ilPez00/cyclops-wearable/cad/pendant_preview.png

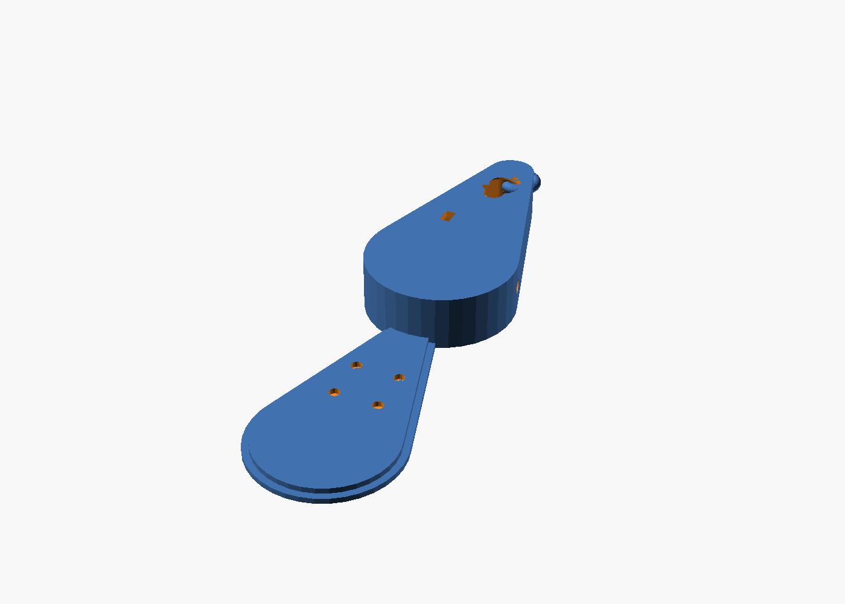
cad/pendant_preview.png
