ilPez00/cyclops-wearable/cad/preview_xiao.png

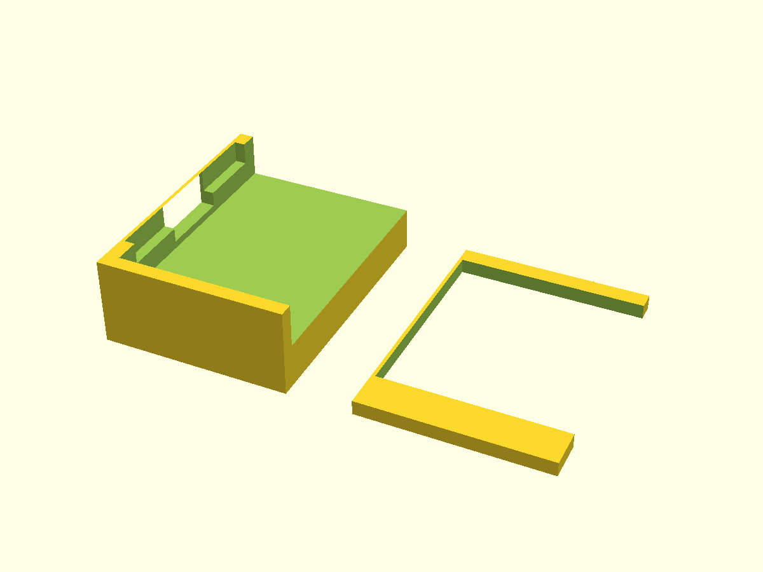
cad/preview_xiao.png
