ilPez00/cyclops-wearable/cad/preview_xiao_v1_pebble.png

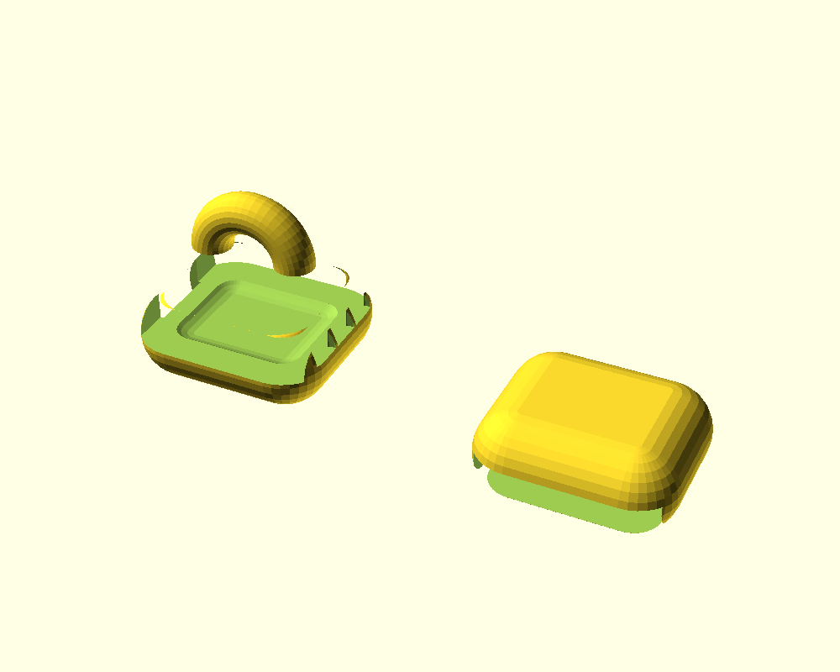
cad/preview_xiao_v1_pebble.png
