ilPez00/cyclops-wearable/cad/preview_xiao_v2_leaf.png

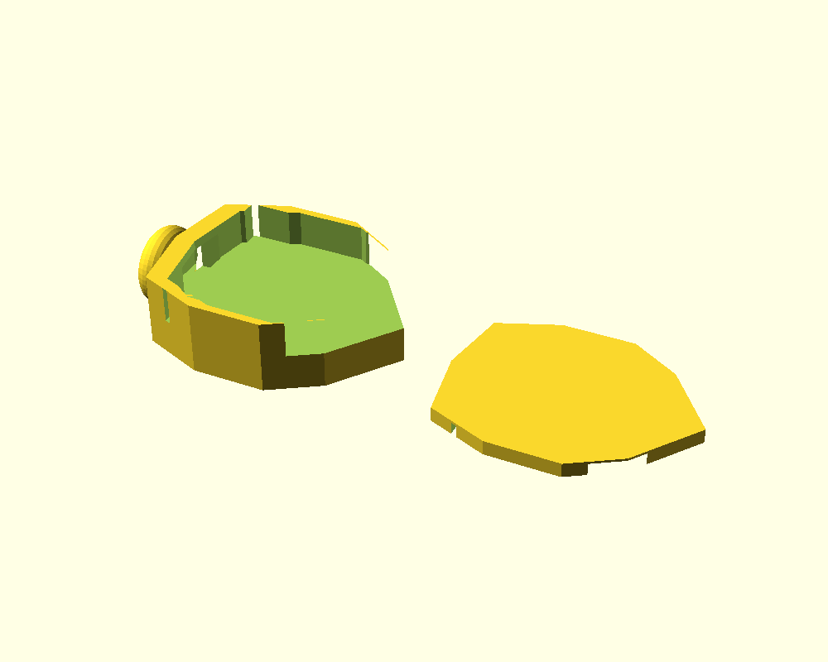
cad/preview_xiao_v2_leaf.png
