ilPez00/cyclops-wearable/cad/preview_xiao_v3_gem.png

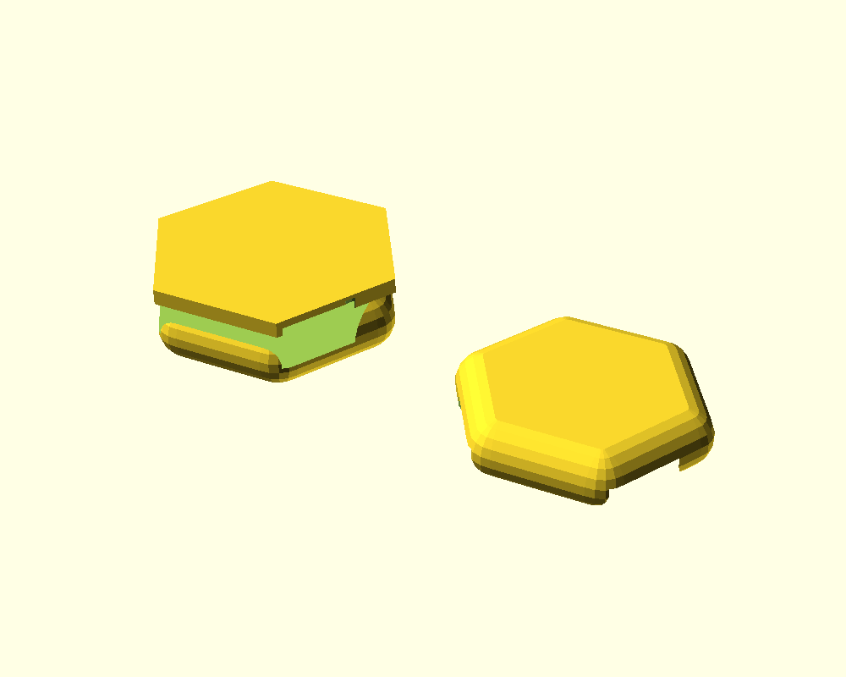
cad/preview_xiao_v3_gem.png
