ilPez00/cyclops-wearable/cad/preview_xiao_v4_temple.png

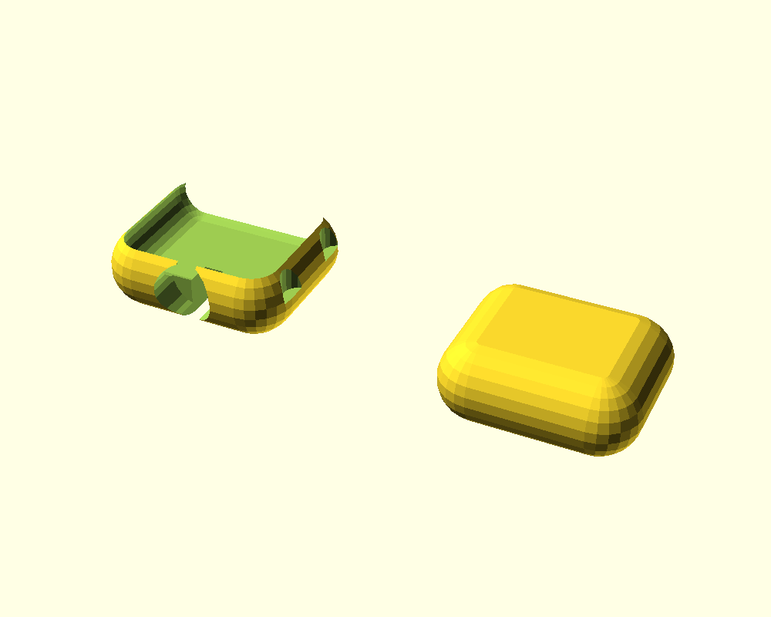
cad/preview_xiao_v4_temple.png
