ilPez00/cyclops-wearable/cad/variants/preview_xiao_pebble.png

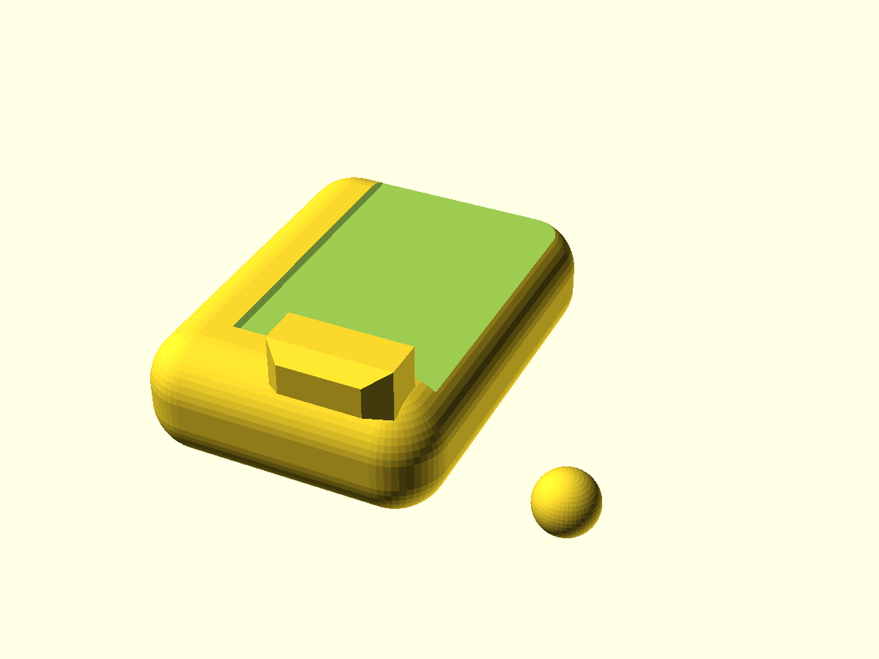
cad/variants/preview_xiao_pebble.png
