ilPez00/cyclops-wearable/cad/variants/preview_xiao_skeleton.png

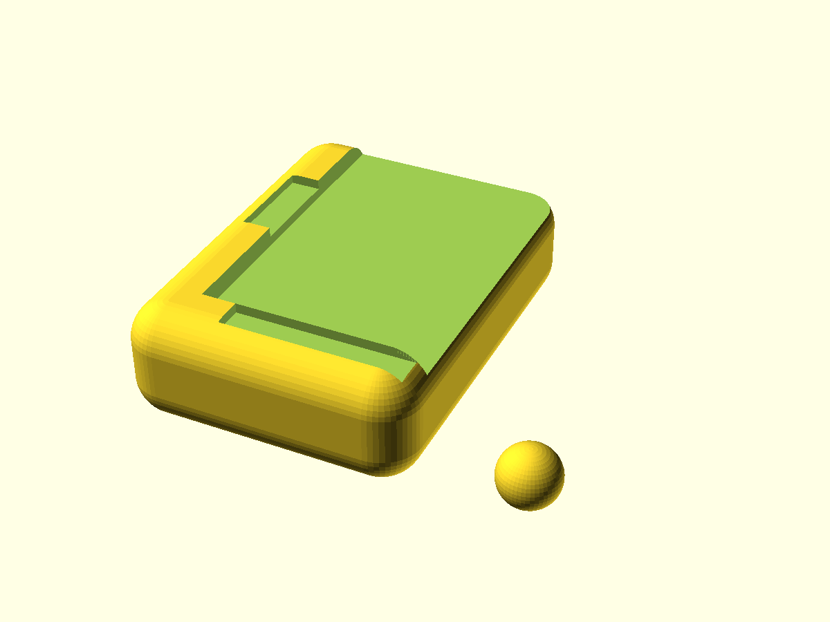
cad/variants/preview_xiao_skeleton.png
