ilPez00/cyclops-wearable/cad/variants/preview_xiao_tech.png

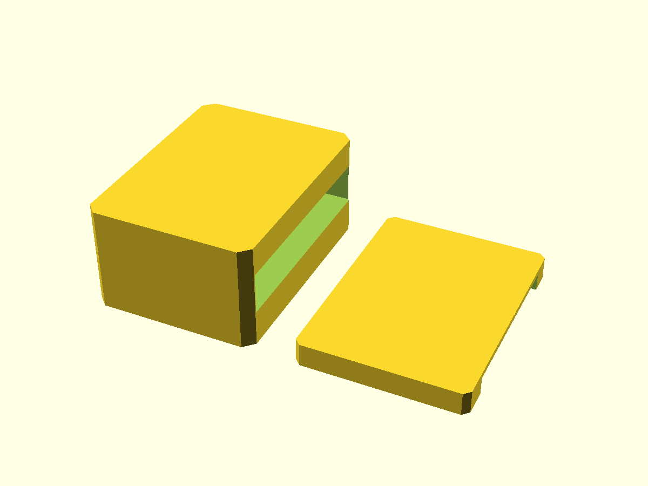
cad/variants/preview_xiao_tech.png
