ilPez00/cyclops-wearable/cad/stl/pendant_v3_antenna_body.stl

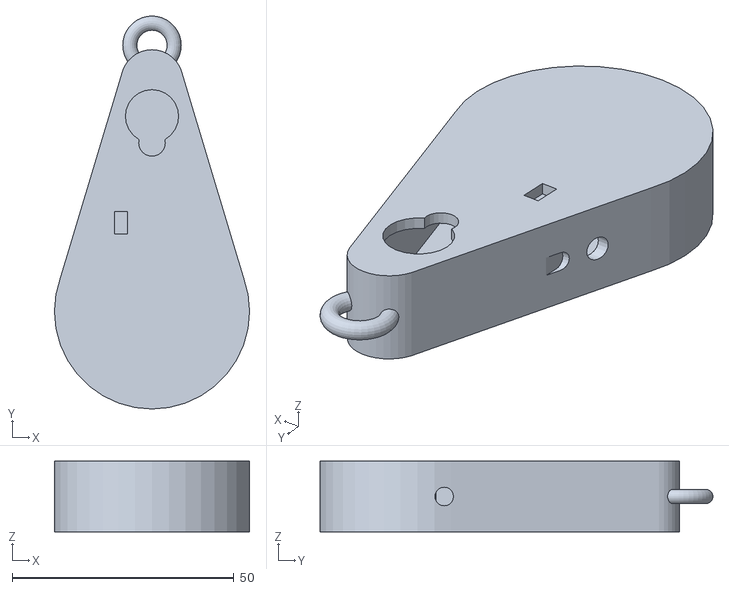
[picture p27: CAD file, 2026-07-10]
cad/stl/pendant_v3_antenna_body.stl
44.0 x 88.6 x 16.0
