ilPez00/cyclops-wearable/cad/stl/pendant_cap.stl

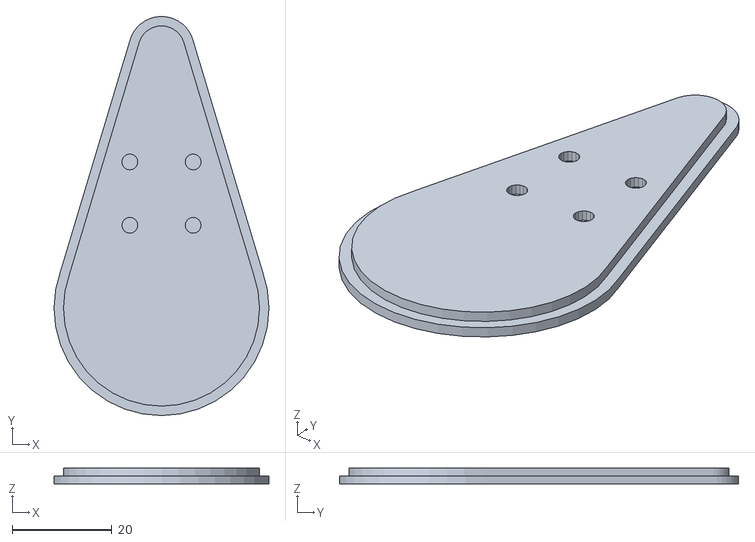
[picture p28: CAD file, 2026-07-10]
cad/stl/pendant_cap.stl
43.2 x 80.2 x 3.20
