ilPez00/cyclops-wearable/cad/stl/v2_body.stl

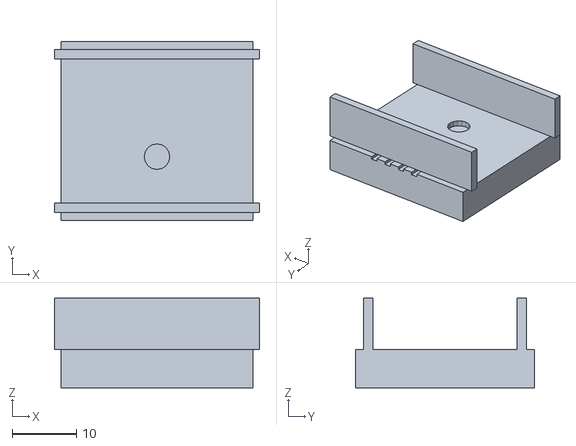
[picture p29: CAD file, 2026-07-10]
cad/stl/v2_body.stl
32.0 x 28.0 x 14.0
