ilPez00/cyclops-wearable/cad/stl/v2_lid.stl

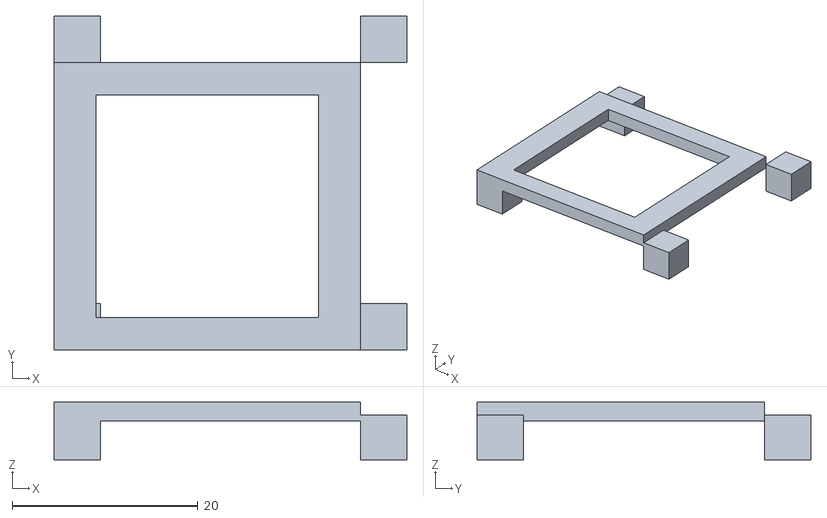
[picture p30: CAD file, 2026-07-10]
cad/stl/v2_lid.stl
38.0 x 36.0 x 6.20
