ilPez00/cyclops-wearable/cad/stl/v2_all.stl

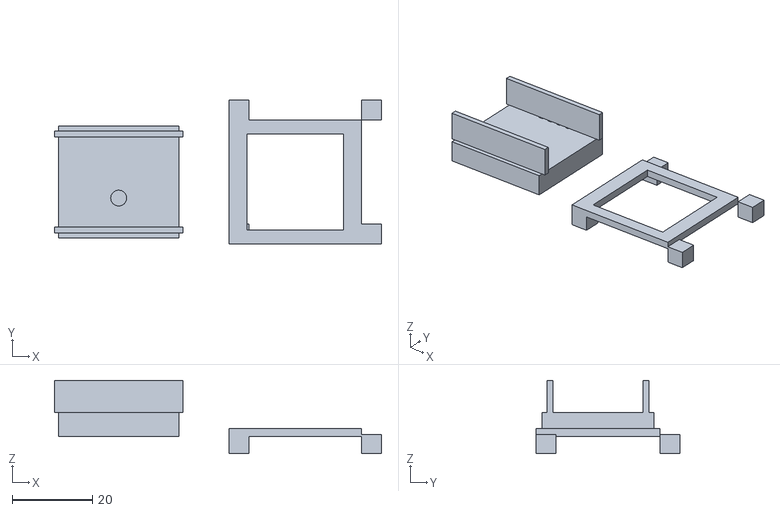
[picture p31: CAD file, 2026-07-10]
cad/stl/v2_all.stl
81.5 x 36.0 x 18.2
