ilPez00/cyclops-wearable/cad/stl/xiao_v4_temple_lid.stl

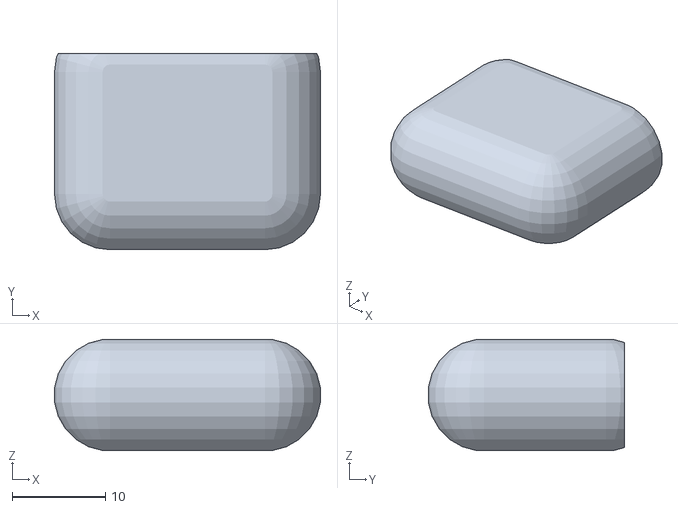
[picture p32: CAD file, 2026-07-09]
cad/stl/xiao_v4_temple_lid.stl
28.5 x 21.0 x 11.9
