ilPez00/cyclops-wearable/cad/stl/xiao_v2_leaf_lid.stl

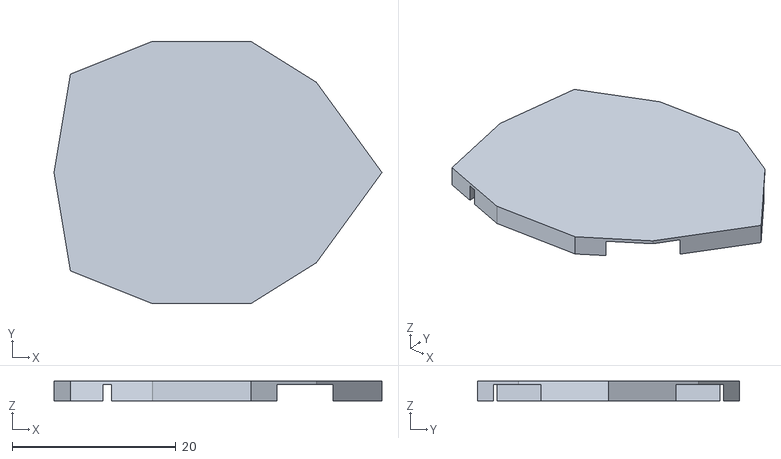
[picture p33: CAD file, 2026-07-09]
cad/stl/xiao_v2_leaf_lid.stl
40.0 x 32.0 x 2.40
