ilPez00/cyclops-wearable/cad/stl/xiao_v3_gem_lid.stl

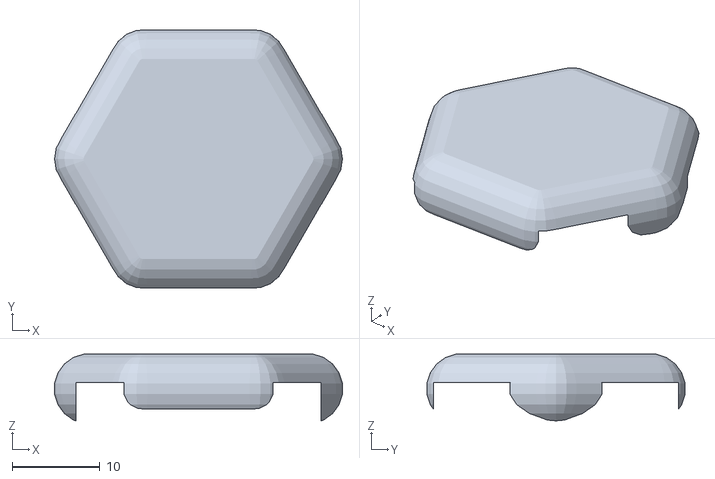
[picture p34: CAD file, 2026-07-09]
cad/stl/xiao_v3_gem_lid.stl
32.9 x 29.5 x 7.62
