ilPez00/cyclops-wearable/cad/stl/xiao_v2_leaf_body.stl

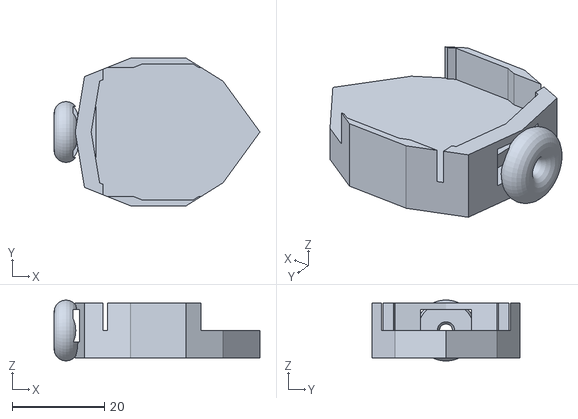
[picture p35: CAD file, 2026-07-09]
cad/stl/xiao_v2_leaf_body.stl
44.6 x 32.0 x 13.2
