ilPez00/cyclops-wearable/cad/stl/xiao_v3_gem_body.stl

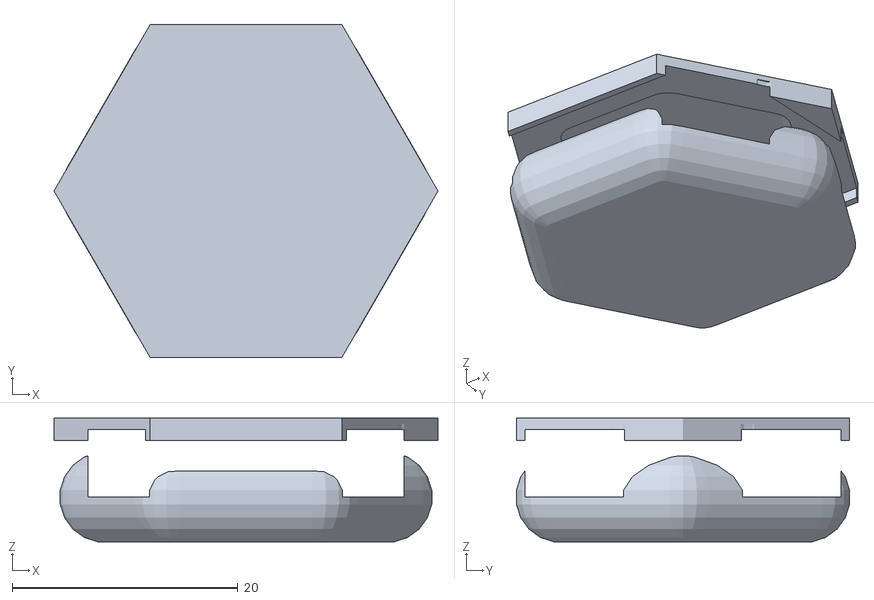
[picture p36: CAD file, 2026-07-09]
cad/stl/xiao_v3_gem_body.stl
34.0 x 29.5 x 11.0
