ilPez00/cyclops-wearable/cad/stl/xiao_v1_pebble_lid.stl

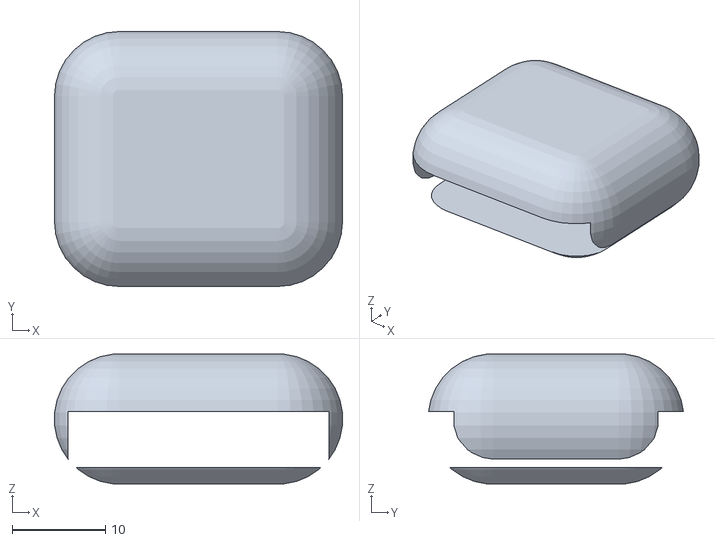
[picture p37: CAD file, 2026-07-09]
cad/stl/xiao_v1_pebble_lid.stl
30.9 x 27.4 x 13.9
