ilPez00/cyclops-wearable/cad/stl/xiao_v4_temple_body.stl

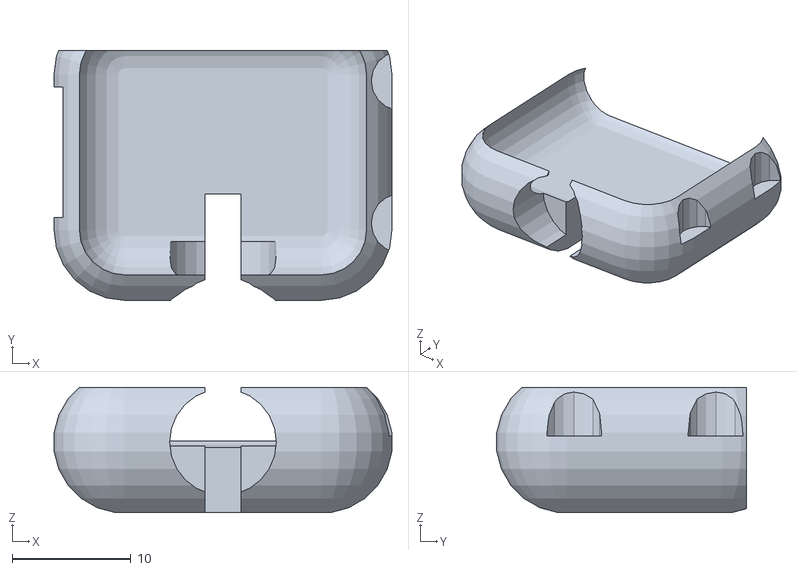
[picture p38: CAD file, 2026-07-09]
cad/stl/xiao_v4_temple_body.stl
28.5 x 21.0 x 10.6
