ilPez00/cyclops-wearable/cad/stl/xiao_all.stl

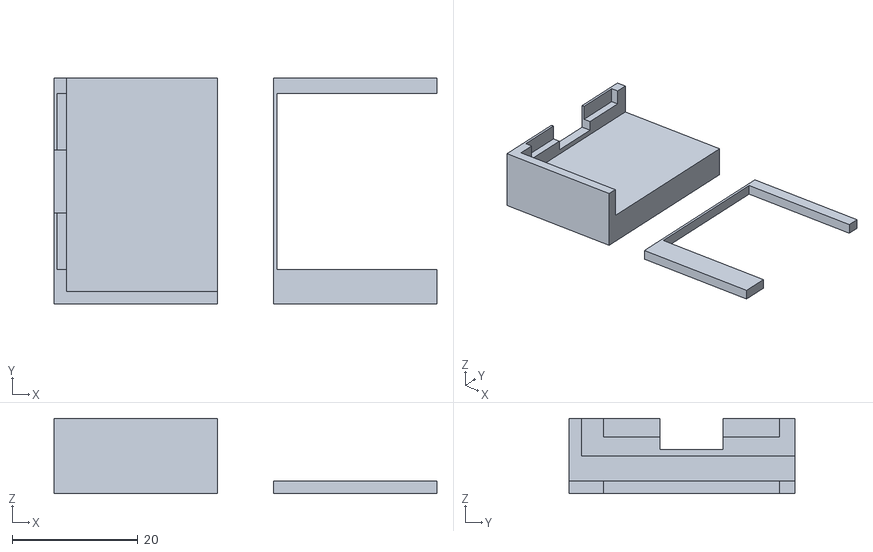
[picture p40: CAD file, 2026-07-09]
cad/stl/xiao_all.stl
61.0 x 36.0 x 12.0
