ilPez00/cyclops-wearable/cad/stl/arduino_all.stl

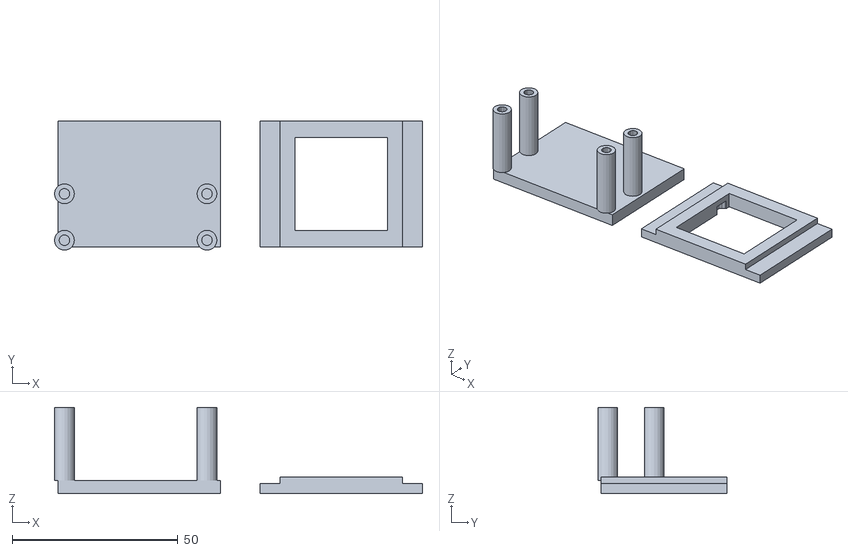
[picture p41: CAD file, 2026-07-09]
cad/stl/arduino_all.stl
111.0 x 39.0 x 26.0
