ilPez00/cyclops-wearable/cad/stl/arduino_body.stl

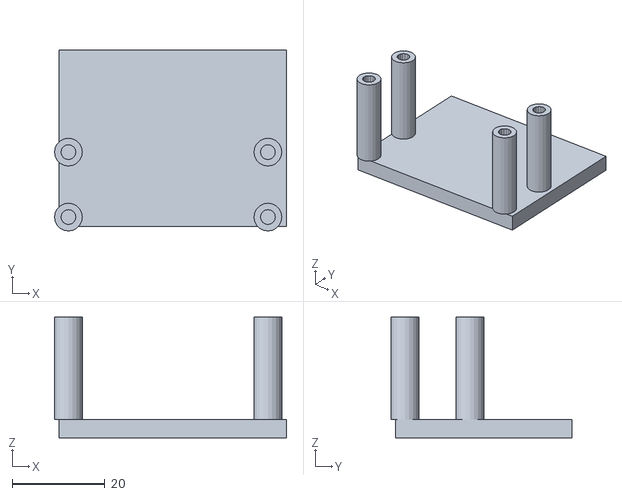
[picture p42: CAD file, 2026-07-09]
cad/stl/arduino_body.stl
50.0 x 39.0 x 26.0
