ilPez00/cyclops-wearable/cad/stl/arduino_lid.stl

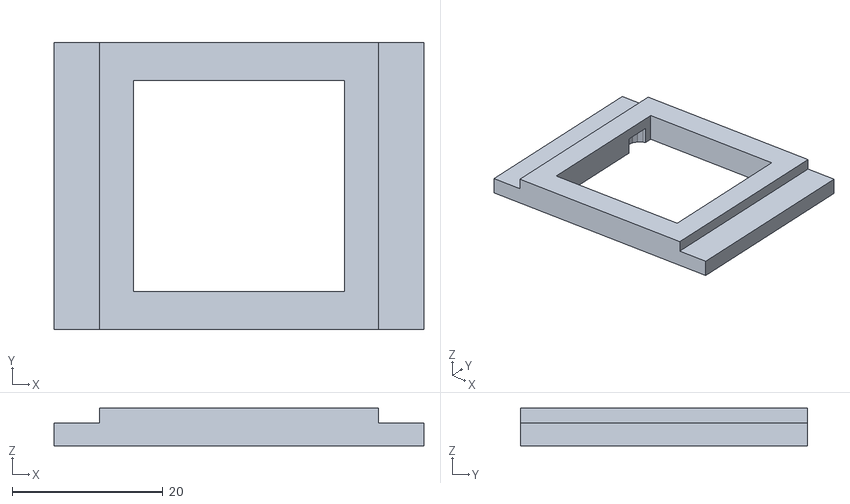
[picture p43: CAD file, 2026-07-09]
cad/stl/arduino_lid.stl
49.0 x 38.0 x 5.00
