ilPez00/cyclops-wearable/cad/stl/xiao_body.stl

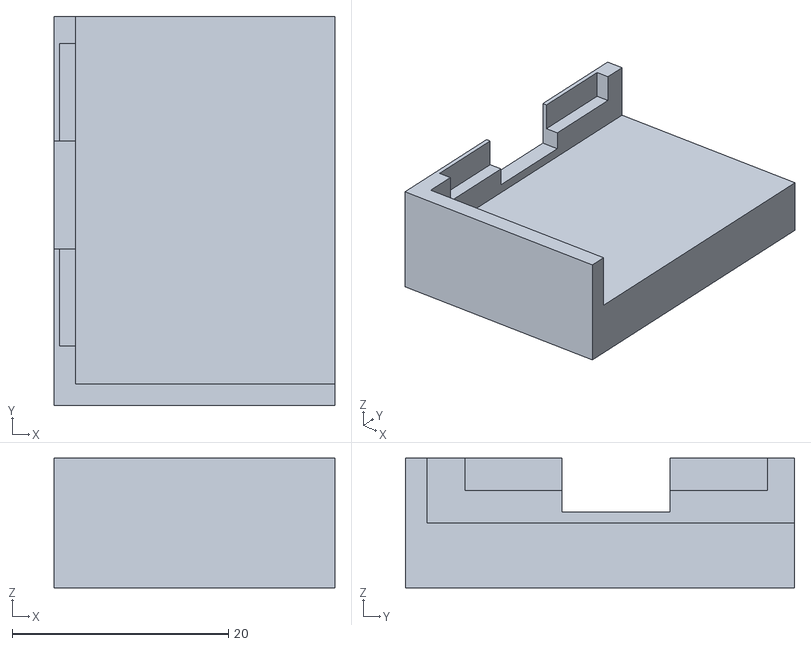
[picture p44: CAD file, 2026-07-09]
cad/stl/xiao_body.stl
26.0 x 36.0 x 12.0
