ilPez00/cyclops-wearable/cad/stl/xiao_lid.stl

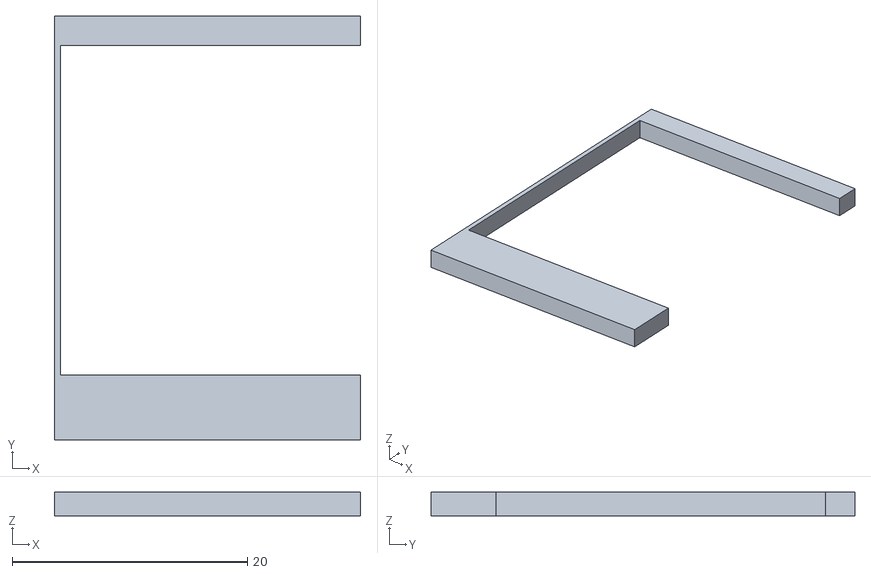
[picture p45: CAD file, 2026-07-09]
cad/stl/xiao_lid.stl
26.0 x 36.0 x 2.00
