ilPez00/cyclops-wearable/docs/cyclops_v1_CyclUno_ASSEMBLY.png

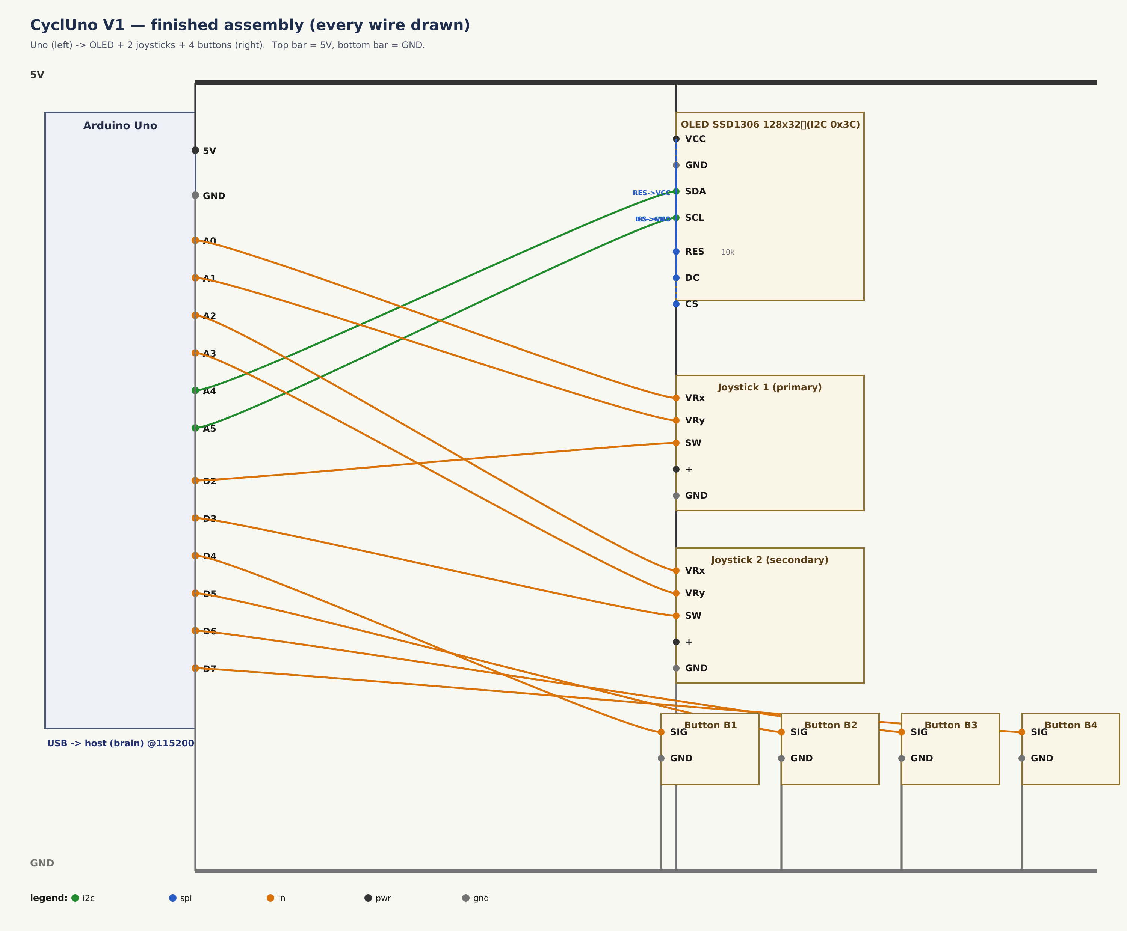
docs/cyclops_v1_CyclUno_ASSEMBLY.png
