ilPez00/cyclops-wearable/docs/cyclops_wiring.png

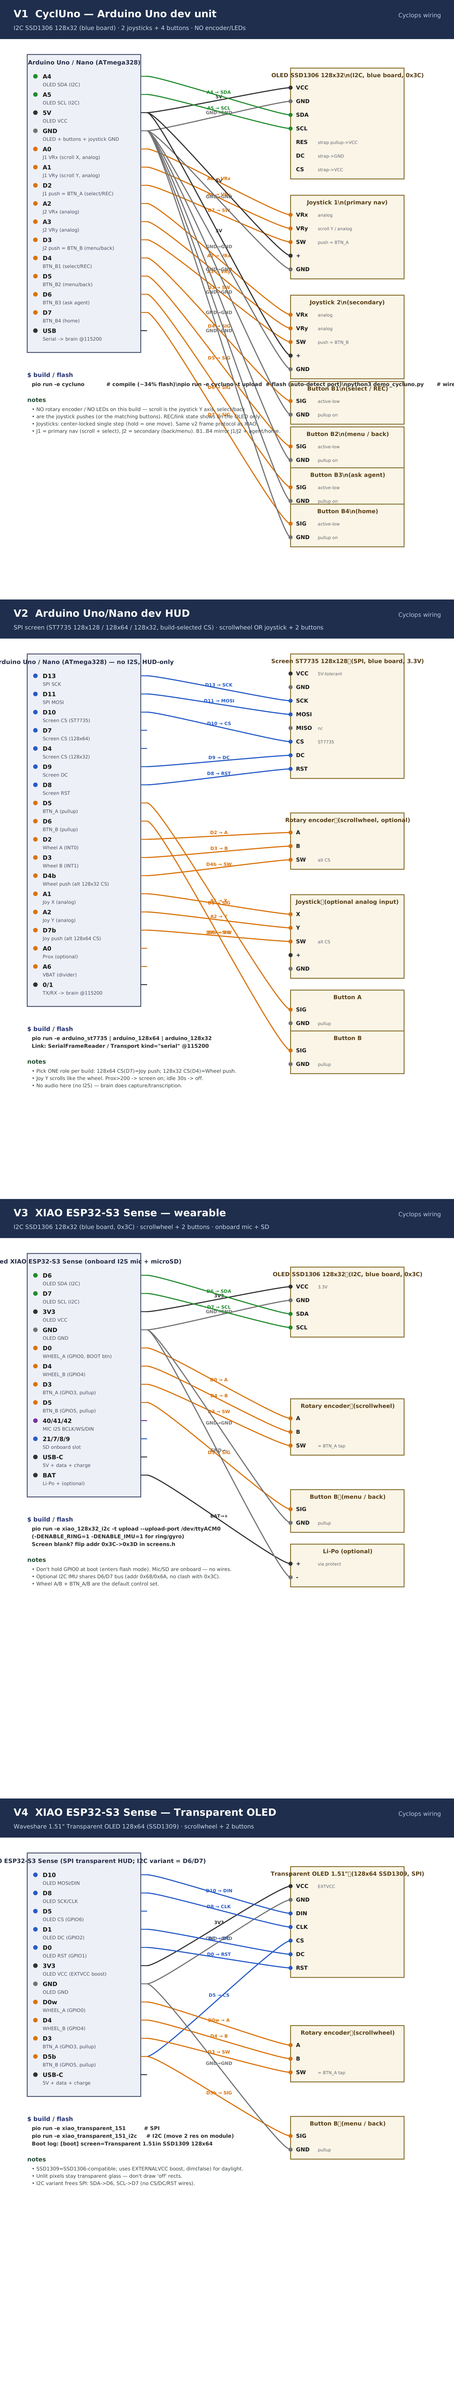
docs/cyclops_wiring.png
