ilPez00/cyclops-wearable/firmware/shared/include/hud.h

#ifndef CYCLOPS_HUD_H
#define CYCLOPS_HUD_H
// HUD + menu system (resolution-agnostic). Thin client: sends MSG_CMD, renders
// results streamed back as DISPLAY_CMD / HUD_FRAME. Host-testable, no display dep.
//
// UX model (XIAO ESP32-S3 Sense + round/e-ink screen + scrollwheel + buttons):
//   HOME  -> glanceable banner (the AI's last line) + status. wheel opens MENU.
//   AGENT -> ask the brain/agent; streams the answer into DETAIL (the "answer" view).
//   Every view shows a 1-line mode breadcrumb in the status bar and transient toasts.
#include "cyclops_shared.h"
#include <stdint.h>
#include <stdlib.h>  // AVR/Arduino-safe; declares atoi
#include <cmath>    // sinf/cosf for arc drawing

namespace cyclops {

enum Mode : uint8_t {
    HOME=0, MENU, NOTES, NOTE_DETAIL, TRANSCRIBE, TRANSLATE,
    HEALTH, TELEPROMPTER, NAV, CAMERA, IMAGE_ANALYSIS, SSH, SETTINGS, CONFIRM,
    CHOICE, AGENT
};

// Action ids sent to the brain via MSG_CMD
enum Action : uint8_t {
    ACT_NOTES=1, ACT_TRANSCRIBE_START=2, ACT_TRANSLATE=3, ACT_HEALTH=4,
    ACT_NAV=5, ACT_TELEPROMPTER=6, ACT_CAMERA=7, ACT_IMAGE_ANALYSIS=8,
    ACT_SSH=9, ACT_SETTINGS=10, ACT_CONFIRM_YES=11, ACT_CONFIRM_NO=12,
    ACT_SELECT=13, ACT_AGENT=14, ACT_AGENT_ABORT=15,
    ACT_PHOTO=16, ACT_VIDEO=17, ACT_VOICE_NOTE=18, ACT_VOICE_CMD=19,
    ACT_OK=20, ACT_BACK=21, ACT_CONSENT_TOGGLE=22, ACT_CHOICE_SELECT=23
};

// Two buttons x three gestures = the remappable binding grid. Index:
// [button 0=A/1=B][gesture 1=single/2=double/3=long]. Defaults implement the
// "eye" (A: ok/photo/video) + "ear" (B: back/voice-note/voice-cmd) scheme;
// the app overrides any cell via a DISPLAY_CMD {"kind":"bind",...}.
struct BtnBindings {
    uint8_t a[4] = { 0, ACT_OK,   ACT_PHOTO,      ACT_VIDEO     };  // [_,single,double,long]
    uint8_t b[4] = { 0, ACT_BACK, ACT_VOICE_NOTE, ACT_VOICE_CMD };
    uint8_t& cell(int btn, int g) { return btn == 0 ? a[g] : b[g]; }
};

struct Hud {
    static const int MAX_NOTES = 12;
    static const int NCOLS = 23;
    static const int DETAIL = 1024;     // agent answers need room
    static const int HUD_LINE = 96;     // glanceable banner (Omi/G2 style)
    static const int TOAST = 48;
    static const int STACK = 6;

    char notes[MAX_NOTES][NCOLS+1];
    int note_count = 0;
    int note_sel = 0;

    // ---- Notification ring buffer (Talon-HUD inspired) ----
    // Transient system notifications with auto-clear TTL. Permanent notes
    // (brain/agent) stay in notes[] and never expire; these are the
    // "system audit" / status pings that should auto-clear after N seconds.
    enum NoteKind : uint8_t { NOTE_INFO=0, NOTE_WARN=1, NOTE_ERR=2, NOTE_OK=3 };
    struct NoteSlot {
        char text[NCOLS+1];
        uint8_t ttl;   // seconds remaining; 0 = slot free/expired
        uint8_t kind;
    };
    static const int RING_SIZE = 8;
    NoteSlot notifs[RING_SIZE];
    uint8_t notif_wp = 0;    // next write position (circular)
    uint8_t notif_count = 0;

    // Push a transient notification. ttl=0 means "keep until overwritten"
    // (rare); default 3s auto-clears. kind drives the glyph in render().
    // notif_count tracks ACTIVE (ttl>0) slots; filling a free/expired slot
    // bumps it, evicting an already-active slot leaves it unchanged (ring).
    void notify(const char* t, uint8_t kind = NOTE_INFO, int ttl = 3) {
        NoteSlot& s = notifs[notif_wp];
        if (s.ttl == 0 && notif_count < RING_SIZE) ++notif_count;  // filling free slot
        int n = 0; while (t && t[n] && n < NCOLS) { s.text[n] = t[n]; ++n; }
        s.text[n] = 0; s.ttl = (uint8_t)ttl; s.kind = kind;
        notif_wp = (uint8_t)((notif_wp + 1) % RING_SIZE);
        if (on_note) on_note(s.text);
    }

    // For a result that completes asynchronously, after do_action() already
    // returned (e.g. a capture finished on a later loop() tick, not
    // synchronously inside the triggering action) -- same wire effect as
    // the private cmd(), public because the caller isn't reacting to a menu
    // action in progress, it's reporting a result that happened later.
    void notify_result(uint8_t a, const char* arg = nullptr) { cmd(a, arg); }

    Mode stack[STACK];
    int sp = 0;                  // top = stack[sp-1]
    int menu_sel = 0;
    const char* menu_items[12] = {
        "Notes","Agent","Transcribe","Translate","Health","Navigate",
        "Teleprompter","Camera","ImageAnalyze","SSH","Settings","Back"
    };
    int menu_n = 12;

    char detail[DETAIL];
    int detail_len = 0;
    int scroll_off = 0;

    char hud_line[HUD_LINE];     // glanceable banner, rendered on HOME + footer
    int hud_len = 0;

    char toast_msg[TOAST];       // transient status ("sent", "thinking…")
    int toast_ttl = 0;       // seconds remaining

    int progress = 0;            // agent/tool progress 0..100 (bar)
    char steps[8][12];       // tool-step ticks (·device ·web …)
    int step_n = 0;

    int sleep_after = 8;     // idle seconds before auto-sleep (OLED burn-in)
    int idle = 0;            // idle counter since last input

    int hr = 0, spo2 = 0, ring_batt = 0, bead_batt = 0;
    int nav_dist = 0, nav_head = 0; char nav_label[24] = "";
    int tele_page = 0;
    char confirm_prompt[32] = ""; uint8_t confirm_action = 0;

    // ---- Choice menu (Talon-HUD inspired) ----
    // Dynamic multi-option list pushed by the brain. Wheel scrolls,
    // select fires ACT_CHOICE_SELECT with the choice's callback tag.
    static const int MAX_CHOICES = 6;
    char choices[MAX_CHOICES][NCOLS+1];
    char choice_cb[32];            // callback tag sent back on select
    int choice_n = 0;
    int choice_sel = 0;
    // Push a choice list. items[] are labels (<=NCOLS chars), cb is the
    // tag the wearable returns to the brain on selection.
    void show_choices(const char* const items[], int n, const char* cb) {
        choice_n = 0; choice_sel = 0;
        int m = (n < MAX_CHOICES) ? n : MAX_CHOICES;
        for (int i = 0; i < m; ++i) {
            int k = 0; while (items[i] && items[i][k] && k < NCOLS) { choices[choice_n][k] = items[i][k]; ++k; }
            choices[choice_n][k] = 0; ++choice_n;
        }
        int c = 0; while (cb && cb[c] && c < 31) { choice_cb[c] = cb[c]; ++c; } choice_cb[c] = 0;
        push(CHOICE);
    }
    int rec_secs = 0;
    int haptic_pattern[2] = {1, 2};   // per-button (A=0,B=1) vibration pattern id
    int led_hue[2] = {0, 200};        // per-button LED hue (0..360) for the paired LED
    Mode prev_mode = HOME;    // last-rendered mode, for transition wipe
    int trans_frame = 0;        // transition wipe frame counter (0..3)
    int low_frame = 0;        // low-battery flash counter (member: template statics diverge per screen type)
    int rec_pulse = 0;        // REC indicator pulse counter (member for the same reason)
    uint32_t clock = 0;
    bool recording = false, screen_on = true, bt = false, consent = true;
    bool charging = false;            // bead/ring battery charging state
    bool video = false;              // video capture active (A-long)
    int boot_frame = 0;              // 0..3 boot spinner, then settled
    BtnBindings bindings;            // remappable 2x3 button grid (app-configurable)

    // callbacks: send a command byte to the brain (BLE/USB). Set by main.
    void (*send_cmd)(uint8_t act, const char* arg) = nullptr;
    void (*on_transcribe_toggle)() = nullptr;  // device starts/stops mic capture
    // Device captures + serves one JPEG frame (#1); returns the capture URL,
    // or "" on failure (no wifi.txt / camera fail) -- cmd()'s arg either way.
    const char* (*on_photo)() = nullptr;
    void (*on_agent_request)(const char* prompt) = nullptr;  // host streams answer via set_agent()
    void (*on_note)(const char* text) = nullptr;  // fired when a note line is added (SD/log sink)
    // MSG_STATUS frame (t=8). v2 adds mode/spo2/prog/toast/recs/steps while
    // keeping the v1 keys (batt/chg/rec/bt/hr) so older parsers still work.
    int status_json(char* out, size_t cap) const {
        const char* m = mode_name(top());
        int n = snprintf(out, cap,
            "{\"t\":8,\"batt\":%u,\"chg\":%d,\"rec\":%d,\"bt\":%d,\"hr\":%d,"
            "\"spo2\":%d,\"mode\":\"%s\",\"prog\":%d,\"recs\":%d,\"toast\":\"%s\"}",
            (unsigned)bead_batt, charging?1:0, recording?1:0, bt?1:0, hr,
            spo2, m, progress, rec_secs,
            toast_ttl > 0 ? toast_msg : "");
        // snprintf returns the WOULD-BE length; callers put `n` bytes on the
        // wire, so an undersized buffer used to leak `n - cap` bytes of
        // garbage past the truncated JSON. Clamp to what was written.
        if (n < 0) return 0;
        return n >= (int)cap ? (int)cap - 1 : n;
    }

    void init() {
        sp = 0; push(HOME); note_count = 0; menu_sel = 0; hud_len = 0; toast_ttl = 0;
        notif_wp = 0; notif_count = 0;
        for (uint8_t i = 0; i < RING_SIZE; ++i) { notifs[i].ttl = 0; notifs[i].kind = NOTE_INFO; notifs[i].text[0] = 0; }
    }
    void push(Mode m) { if (sp < STACK) stack[sp++] = m; }
    Mode top() const { return sp > 0 ? stack[sp-1] : HOME; }
    void pop() { if (sp > 1) --sp; }
    void home() { sp = 0; push(HOME); }

    void add_note(const char* t) {
        if (note_count >= MAX_NOTES) { memmove(notes[0], notes[1], (MAX_NOTES-1)*(NCOLS+1)); note_count = MAX_NOTES-1; }
        int n = 0; while (t[n] && n < NCOLS) { notes[note_count][n] = t[n]; ++n; }
        notes[note_count][n] = 0; note_count++;
        if (on_note) on_note(notes[note_count-1]);
    }
    void set_detail(const char* t) {
        detail_len = 0; while (t && t[detail_len] && detail_len < DETAIL-1) { detail[detail_len] = t[detail_len]; ++detail_len; }
        detail[detail_len] = 0; scroll_off = 0;
    }
    // Push a glanceable banner line (the AI's last words). Shown on HOME + footer.
    void set_hud(const char* t) {
        hud_len = 0; while (t && t[hud_len] && hud_len < HUD_LINE-1) { hud_line[hud_len] = t[hud_len]; ++hud_len; }
        hud_line[hud_len] = 0;
    }
    // Stream an agent answer (keeps appending, capped at DETAIL).
    void append_agent(const char* chunk) {
        while (chunk && *chunk && detail_len < DETAIL-1) { detail[detail_len++] = *chunk++; }
        detail[detail_len] = 0;
    }
    void toast(const char* msg, int ttl = 2) {
        int n = 0; while (msg && msg[n] && n < TOAST-1) { toast_msg[n] = msg[n]; ++n; }
        toast_msg[n] = 0; toast_ttl = ttl;
    }
    void wake() { idle = 0; screen_on = true; }
    void add_step(const char* tool) {
        if (step_n >= 8) return;
        int n = 0; while (tool && tool[n] && n < 11) { steps[step_n][n] = tool[n]; ++n; }
        steps[step_n][n] = 0; step_n++;
    }
    void set_progress(int p) { progress = clamp(p, 0, 100); }
    void set_consent(bool c) { consent = c; }
    // Parse a DISPLAY_CMD JSON from the brain and update Hud state.
    // Handles {"kind":"progress","p":NN}, {"kind":"step","tool":"x"},
    // and default {"kind":"text"/"data"/"text":...} -> add_note.
    void apply_display_cmd(const char* json) {
        const char* k = strstr(json, "\"kind\"");
        if (k) {
            if (strstr(k, "\"progress\"")) {
                const char* p = strstr(k, "\"p\":");
                if (p) set_progress(atoi(p + 4));
                return;
            }
            if (strstr(k, "\"step\"")) {
                const char* t = strstr(k, "\"tool\"");
                if (t) { const char* s = strchr(t, ':'); if (s) { ++s; while (*s==' '||*s=='\"') ++s;
                    char buf[12]; int i=0; while (*s && *s!='\"' && *s!=',' && i<11) buf[i++]=*s++; buf[i]=0; if (buf[0]) add_step(buf); } }
                return;
            }
            if (strstr(k, "\"consent\"")) {
                const char* v = strstr(k, "\"on\"");
                set_consent(v ? atoi(v + 5) != 0 : true);
                return;
            }
            if (strstr(k, "\"bind\"")) {
                const char* pb = strstr(k, "\"btn\":");
                const char* pg = strstr(k, "\"g\":");
                const char* pa = strstr(k, "\"act\":");
                if (pb && pg && pa) set_binding(atoi(pb+6), atoi(pg+4), (uint8_t)atoi(pa+6));
                return;
            }
        }
        // dynamic choice list (Talon-HUD choice panel)
        if (strstr(k, "\"choices\"")) {
            const char* cb = strstr(k, "\"cb\"");
            char cbtag[32]; cbtag[0]=0;
            if (cb) { const char* s = strchr(cb, ':'); if (s) { ++s; while (*s==' '||*s=='\"') ++s;
                int i=0; while (*s && *s!='\"' && *s!=',' && i<31) cbtag[i++]=*s++; cbtag[i]=0; } }
            // parse up to MAX_CHOICES labels from "items":["a","b",...]
            // static scratch buffers (no strndup; ESP32 libc lacks it)
            static char cbuf[6][24];
            const char* items = strstr(k, "\"items\"");
            const char* arr = items ? strchr(items, '[') : nullptr;
            const char* list[6]; int ln2 = 0;
            if (arr) { const char* p = arr + 1;
                while (*p && *p != ']' && ln2 < 6) {
                    while (*p && *p != '\"') ++p;
                    if (!*p) break; ++p;
                    int bi=0; while (*p && *p!='\"' && bi<23) cbuf[ln2][bi++]=*p++; cbuf[ln2][bi]=0;
                    if (*p) ++p;  // skip closing quote
                    if (cbuf[ln2][0]) { list[ln2] = cbuf[ln2]; ++ln2; }
                }
            }
            show_choices(list, ln2, cbtag[0] ? cbtag : "choice");
            return;
        }
        // default: treat as a text line -> note
        const char* key = strstr(json, "\"data\"") ? "\"data\"" : "\"text\"";
        const char* t = strstr(json, key);
        if (!t) return;
        const char* s = strchr(t, ':'); if (!s) return; ++s;
        while (*s==' ') ++s;
        if (*s=='"') { ++s; char out[64]; int i=0; while (*s && *s!='"' && i<63) out[i++]=*s++; out[i]=0; add_note(out); }
    }
    // Advance 1s of wall clock (REC timer + toast + notif TTL + idle sleep).
    void tick_sec() {
        if (recording) ++rec_secs;
        if (toast_ttl > 0) --toast_ttl;
        // expire notification slots whose TTL ran out
        for (uint8_t i = 0; i < RING_SIZE; ++i) {
            if (notifs[i].ttl > 0) { if (--notifs[i].ttl == 0 && notif_count > 0) --notif_count; }
        }
        if (boot_frame < 4) ++boot_frame;     // ~4s boot spinner, then settled
        if (screen_on) { if (++idle >= sleep_after) screen_on = false; }
    }

    void request_confirm(const char* prompt, uint8_t action) {
        strncpy(confirm_prompt, prompt ? prompt : "", 31); confirm_prompt[31] = 0;
        confirm_action = action; push(CONFIRM);
    }

    // ---- input handlers ----
    void on_wheel(int d) {
        wake();
        Mode m = top();
        if (m == MENU) menu_sel = clamp(menu_sel + d, 0, menu_n-1);
        else if (m == NOTES) note_sel = clamp(note_sel + d, 0, note_count-1);
        else if (m == CHOICE) choice_sel = clamp(choice_sel + d, 0, choice_n-1);
        else if (m == NOTE_DETAIL || m == TRANSLATE || m == IMAGE_ANALYSIS || m == SSH || m == CAMERA || m == AGENT)
            scroll_off = clamp(scroll_off + d*16, 0, detail_len);
        else if (m == TELEPROMPTER) tele_page = clamp(tele_page + d, 0, 999);
    }
    void on_select() {
        wake();
        Mode m = top();
        if (m == MENU) {
            const char* act = menu_items[menu_sel];
            if (!strcmp(act, "Back")) pop();
            else if (!strcmp(act, "Notes")) push(NOTES);
            else if (!strcmp(act, "Agent")) { set_detail(""); scroll_off = 0; push(AGENT);
                                               toast("ask via app/voice", 2); }
            else if (!strcmp(act, "Transcribe")) { if (!consent) { toast("consent off", 2); return; } recording = true; rec_secs = 0; push(TRANSCRIBE); cmd(ACT_TRANSCRIBE_START); if (on_transcribe_toggle) on_transcribe_toggle(); }
            else if (!strcmp(act, "Translate")) { set_detail(note_count ? notes[note_sel] : ""); push(TRANSLATE); cmd(ACT_TRANSLATE, note_count ? notes[note_sel] : ""); }
            else if (!strcmp(act, "Health")) push(HEALTH);
            else if (!strcmp(act, "Navigate")) push(NAV);
            else if (!strcmp(act, "Teleprompter")) { tele_page = 0; push(TELEPROMPTER); cmd(ACT_TELEPROMPTER); }
            else if (!strcmp(act, "Camera")) { push(CAMERA); cmd(ACT_CAMERA); }
            else if (!strcmp(act, "ImageAnalyze")) { push(IMAGE_ANALYSIS); cmd(ACT_IMAGE_ANALYSIS); }
            else if (!strcmp(act, "SSH")) { push(SSH); cmd(ACT_SSH); }
            else if (!strcmp(act, "Settings")) push(SETTINGS);
        } else if (m == NOTES) {
            if (note_count) { set_detail(notes[note_sel]); push(NOTE_DETAIL); }
        } else if (m == AGENT) {
            // Entering AGENT from the menu opens a fresh query; a real prompt is
            // delivered by the host via on_agent_request() / set_hud().
            toast("agent ready", 2);
        } else if (m == CONFIRM) {
            cmd(ACT_CONFIRM_YES); pop();
        } else if (m == CHOICE) {
            if (choice_n) cmd(ACT_CHOICE_SELECT, choice_cb);
            pop();
        } else if (m == HOME) {
            push(MENU);
        }
    }
    void on_long_back() {
        wake();
        // stop any capture/agent before leaving
        if (top() == TRANSCRIBE && recording) { recording = false; if (on_transcribe_toggle) on_transcribe_toggle(); cmd(ACT_TRANSCRIBE_START); }
        if (top() == AGENT) cmd(ACT_AGENT_ABORT);
        pop();
    }
    // Short cancel (BTN_B / second button). Declines a confirm, else backs out one level.
    void on_cancel() {
        wake();
        Mode m = top();
        if (m == CONFIRM) { cmd(ACT_CONFIRM_NO); pop(); }
        else if (m != HOME) { pop(); }
        else { /* on HOME, cancel is a no-op */ }
    }
    void on_back_gesture() { on_long_back(); }
    // Ring/glasses gesture dispatch (codes mirror protocol_v2.GEST):
    // 1 up, 2 down, 3 select, 4 back, 5 nod, 6 home.
    void on_gesture(int code) {
        wake();
        switch (code) {
            case 1: on_wheel(-1); break;   // up
            case 2: on_wheel(1);  break;   // down
            case 3: on_select();  break;
            case 4: on_long_back(); break;
            case 5: on_nod();     break;
            case 6: home();       break;
            default: break;
        }
    }
    void on_nod() { wake(); if (!recording && !consent) { toast("consent off", 2); return; } recording = !recording; if (recording) { rec_secs = 0; cmd(ACT_TRANSCRIBE_START); if (on_transcribe_toggle) on_transcribe_toggle(); } }   // quick capture toggle

    // ---- button gestures (remappable). btn 0=A, 1=B; g 1=single/2=double/3=long ----
    void set_binding(int btn, int g, uint8_t act) {
        if (btn < 0 || btn > 1 || g < 1 || g > 3) return;
        bindings.cell(btn, g) = act;
    }
    void fire_gesture(int btn, int g) {
        if (btn < 0 || btn > 1 || g < 1 || g > 3) return;
        if (on_haptic) on_haptic(haptic_pattern[btn]);   // buzz the wearer
        if (on_led) on_led(btn, led_hue[btn]);     // flash the paired LED
        do_action(bindings.cell(btn, g));
    }
    // Run one bound action. Menu/nav actions steer the HUD; capture/agent
    // actions gate on consent and notify the brain via cmd().
    void do_action(uint8_t act) {
        wake();
        switch (act) {
            case ACT_OK:     on_select(); break;
            case ACT_BACK:   on_cancel(); break;
            case ACT_PHOTO:
                if (!consent) { toast("consent off", 2); break; }
                toast("photo", 2);
                cmd(ACT_PHOTO, on_photo ? on_photo() : nullptr);
                break;
            case ACT_VIDEO:
                if (!consent) { toast("consent off", 2); break; }
                video = !video; toast(video ? "video on" : "video off", 2); cmd(ACT_VIDEO); break;
            case ACT_VOICE_NOTE:
                if (!consent) { toast("consent off", 2); break; }
                toast("voice note", 2); cmd(ACT_VOICE_NOTE);
                if (on_transcribe_toggle) { on_transcribe_toggle(); }
                break;
            case ACT_VOICE_CMD:
                if (!consent) { toast("consent off", 2); break; }
                toast("listening", 2); set_detail(""); push(AGENT); cmd(ACT_VOICE_CMD);
                if (on_transcribe_toggle) { on_transcribe_toggle(); }
                break;
            case ACT_CONSENT_TOGGLE:
                set_consent(!consent); toast(consent ? "consent on" : "consent off", 2); break;
            default: if (act) cmd(act); break;
        }
    }

    void set_health(int h, int s, int rb, int bb) { hr = h; spo2 = s; ring_batt = rb; bead_batt = bb; }

    // Haptic / LED mapping (per button A=0, B=1), configurable from the app.
    void set_haptic(int btn, int pat) { if (btn >= 0 && btn <= 1) haptic_pattern[btn] = pat; }
    void set_led(int btn, int hue) { if (btn >= 0 && btn <= 1) led_hue[btn] = hue; }
    // hooks wired to real hardware in xiao (no-op here); fire on each gesture.
    void (*on_haptic)(int pattern) = nullptr;
    void (*on_led)(int btn, int hue) = nullptr;
    // Incoming MSG_HEALTH_SAMPLE (phone->wearable relay, P2-C): parse
    // "t=,hr=,spo2=,sl=,batt=" and apply. We only take hr/spo2/ring_batt.
    void on_health_sample(const char* p) {
        auto atoi_k = [&](const char* k) -> int {
            const char* v = strstr(p, k); if (!v) return -1;
            return atoi(v + strlen(k));
        };
        int h = atoi_k("hr="); if (h > 0) hr = h;
        int s = atoi_k("spo2="); if (s > 0) spo2 = s;
        int b = atoi_k("batt="); if (b > 0) ring_batt = b;
        int c = atoi_k("chg="); if (c > 0) charging = true; else if (strstr(p, "chg=0")) charging = false;
    }
    void set_nav(int dist_m, int head, const char* label) { nav_dist = dist_m; nav_head = head; strncpy(nav_label, label?label:"",23); nav_label[23]=0; }
    void set_tele(const char* /*full*/, int page) { tele_page = page; }

    // Ask the agent (from app/voice). Host callback streams the answer back.
    void agent_ask(const char* prompt) {
        wake();
        set_detail(""); scroll_off = 0; step_n = 0; progress = 0;
        if (top() != AGENT) push(AGENT);
        toast("thinking…", 2);
        if (on_agent_request) on_agent_request(prompt ? prompt : "");
    }

    // ---- pixel-graphics helpers (templated on Screen S) ----
    // Pure drawing primitives built on S.draw_pixel / S.draw_line /
    // S.fill_rect. Host-testable: a Screen mock can record the calls.
    template<typename S>
    static void drawArc(S& scr, int cx, int cy, int r, int a0, int a1, int step = 3) {
        for (int a = a0; a <= a1; a += step) {
            float rad = a * 3.14159265f / 180.f;
            int x = cx + (int)(r * sinf(rad));
            int y = cy - (int)(r * cosf(rad));
            scr.draw_pixel(x, y, true);
        }
    }

    // Radial gauge: background arc + filled arc up to [progress] 0..100.
    template<typename S>
    static void drawGauge(S& scr, int cx, int cy, int r, int progress, int gap = 90) {
        int a0 = 90 + gap / 2;          // start (bottom-left gap)
        int a1 = a0 + 360 - gap;        // end (bottom-right gap)
        drawArc(scr, cx, cy, r, a0, a1, 4);                 // track
        int filled = a0 + (int)((360 - gap) * clamp(progress, 0, 100) / 100.f);
        drawArc(scr, cx, cy, r, a0, filled, 4);             // value
    }

    // Horizontal progress bar from (x,y) width w, height h, 0..100.
    template<typename S>
    static void drawProgressBar(S& scr, int x, int y, int w, int h, int progress) {
        scr.draw_rect(x, y, w, h, true);                    // frame
        int fw = (int)((w - 2) * clamp(progress, 0, 100) / 100.f);
        if (fw > 0) scr.fill_rect(x + 1, y + 1, fw, h - 2, true);
    }

    // Battery glyphs: draw bead (main unit, larger) + ring (wearable, smaller)
    // side by side. Flash a '!' when either is critically low (<20%). charging
    // adds a '+' suffix. Monochrome-safe (no emoji).
    template<typename S>
    static void drawBatteryIcon(S& scr, int x, int y, int ring_level, int bead_level, bool charging, int frame) {
        int bl = bead_level > 0 ? bead_level : ring_level;   // effective level
        int rl = ring_level > 0 ? ring_level : bead_level;
        // bead (main): 14x7 body
        scr.draw_rect(x, y, 14, 7, true);
        scr.draw_rect(x + 14, y + 2, 2, 3, true);
        int bw = (int)(12 * clamp(bl, 0, 100) / 100.f);
        if (bw > 0) scr.fill_rect(x + 1, y + 1, bw, 5, true);
        // ring (wearable): 10x5 body
        scr.draw_rect(x + 20, y + 1, 10, 5, true);
        scr.draw_rect(x + 30, y + 2, 1, 3, true);
        int rw = (int)(8 * clamp(rl, 0, 100) / 100.f);
        if (rw > 0) scr.fill_rect(x + 21, y + 2, rw, 3, true);
        // critical low-battery flash
        bool crit = (bl > 0 && bl < 20) || (rl > 0 && rl < 20);
        if (crit && (frame % 8) < 4) scr.draw_text(x + 33, y, "!");
        if (charging) scr.draw_text(x + 33, y, "+");
    }

    // Boot animation frame (spinner). frame 0..3 cycles a sweeping arc.
    template<typename S>
    static void drawBoot(S& scr, int cx, int cy, int r, int frame) {
        int a = (frame % 4) * 90;
        drawArc(scr, cx, cy, r, a, a + 60, 3);
    }

    // ---- render to a Screen ----
    template<typename S>
    void render(S& scr) {
        scr.clear();
        if (!screen_on) { scr.flush(); return; }
        int rows = scr.text_rows();
        int cols = scr.char_cols();
        // status bar row 0: two fixed zones (Talon-HUD style) drawn as one
        // row so the on-screen layout is left=connectivity, right=power:
        //   LEFT  = connectivity (clock + BLE phone + ring/bead link)
        //   RIGHT = power (effective battery % + charging + low-batt warn)
        int eff_batt = bead_batt > 0 ? bead_batt : ring_batt;
        const char* bt_icon  = bt ? "BT+" : "BT-";          // + connected, - not
        const char* ring_link = (ring_batt > 0) ? "RN" : "--";
        const char* bead_link = (bead_batt > 0) ? "BD" : "--";
        const char* chg = charging ? "^" : "";
        const char* low = (eff_batt > 0 && eff_batt < 20) ? "!" : "";  // low-batt warn
        char sb[40];
        int llen = snprintf(sb, sizeof(sb), "%02u:%02u %s %s%s",
                            (clock/3600)%24, (clock/60)%60, bt_icon, ring_link, bead_link);
        // right-justify the power zone at the end of the row
        int rlen = (int)strlen(chg) + (int)strlen(low) + 3; // "NNN%"
        int pad = cols - llen - rlen;
        if (pad < 1) pad = 1;
        snprintf(sb + llen, sizeof(sb) - llen, "%*s%d%%%s%s", pad, "", eff_batt, chg, low);
        scr.set_ink(true); scr.draw_text(0, 0, sb);

        // mode-transition wipe: brief vertical bar sweep on mode change (battery-safe, 4 frames)
        Mode cur = top();
        if (cur != prev_mode) { trans_frame = 0; prev_mode = cur; }
        if (trans_frame < 4 && scr.w() >= 48) {
            int wx = (trans_frame * scr.w()) / 4;
            for (int yy = 1; yy < scr.h(); ++yy) scr.draw_pixel(wx, yy, true);
            ++trans_frame;
        }

        Mode m = top();
        int body = 1;
        // active notification footer (Talon-HUD inspired): newest active notif
        if (notif_count > 0) {
        // find the newest non-expired slot (highest age since write)
        int newest = -1;
        for (uint8_t i = 0; i < RING_SIZE; ++i) if (notifs[i].ttl > 0) newest = i;
        if (newest >= 0) {
            const char* glyph = notifs[newest].kind == NOTE_ERR ? "!" :
                                 notifs[newest].kind == NOTE_WARN ? "*" :
                                 notifs[newest].kind == NOTE_OK   ? "+" : ">";
            char ln[40];
            snprintf(ln, sizeof(ln), "%s %s", glyph, notifs[newest].text);
            trim(ln, cols); scr.draw_text(0, body, ln); body++;
        }
        }
        if (m == HOME) {
            // boot spinner for the first ~2s on pixel-capable panels
            if (boot_frame < 4 && scr.w() >= 48 && scr.h() >= 32) {
                drawBoot(scr, scr.w() / 2, scr.h() / 2, scr.h() / 3, boot_frame);
                char ln[32]; snprintf(ln, sizeof(ln), "Cyclops %d", boot_frame);
                scr.draw_text(0, rows - 1, ln);
            } else if (hud_len) { scr.text_size(2); scr.draw_text(0, body, trunc(hud_line, cols/2)); scr.text_size(1); body++; }
            else { scr.draw_text(0, body, "Cyclops ready"); body++; }
            // LED mapping indicator: per-button hue encoded as a bar on capable panels
            if (scr.w() >= 64) {
                char li[32];
                int wa = (led_hue[0] * 10) / 360;   // 0..10
                int wb = (led_hue[1] * 10) / 360;
                snprintf(li, sizeof(li), "A%d B%d", wa, wb);
                trim(li, cols); scr.draw_text(scr.char_cols() - (int)strlen(li), rows - 1, li);
            }
            // status strip (semantic zone): battery + note count + REC
            char ln[40];
            snprintf(ln, sizeof(ln), "%dmV %d notes%s", (bead_batt>0?bead_batt:ring_batt),
                     note_count, recording ? " REC" : "");
            trim(ln, cols); scr.draw_text(0, body, ln); body++;
            // bottom strip: current mode + primary hint (moved out of status bar).
            // Skip during the boot splash so it doesn't clobber the boot frame.
            bool booting = (boot_frame < 4 && scr.w() >= 48 && scr.h() >= 32);
            if (!booting) {
                char strip[40];
                snprintf(strip, sizeof(strip), "%s | wheel:menu", mode_name(top()));
                trim(strip, cols); scr.draw_text(0, rows - 1, strip);
            }
        } else if (m == MENU) {
            for (int i = 0; i < rows-1 && i < menu_n; ++i) {
                const char* mk = (i == menu_sel) ? ">" : " ";
                char ln[32]; snprintf(ln, sizeof(ln), "%s%s", mk, menu_items[i]);
                trim(ln, cols); scr.draw_text(0, body+i, ln);
            }
            // scroll breadcrumb: vertical bar on right edge at menu_sel position
            if (menu_n > rows - 1) {
                int by = 1 + (menu_sel * (rows - 2)) / menu_n;
                int bh = (rows - 2) / menu_n + 1; if (bh < 1) bh = 1;
                for (int y = by; y < by + bh && y < rows - 1; ++y)
                    scr.draw_pixel(scr.char_cols() - 1, body + y, true);
            }
        } else if (m == NOTES) {
            for (int i = 0; i < rows-1 && i < note_count; ++i) {
                const char* mk = (i == note_sel) ? ">" : " ";
                char ln[40]; snprintf(ln, sizeof(ln), "%s%d %s", mk, i+1, notes[i]);
                trim(ln, cols); scr.draw_text(0, body+i, ln);
            }
        } else if (m == NOTE_DETAIL || m == TRANSLATE || m == IMAGE_ANALYSIS || m == SSH || m == CAMERA) {
            draw_detail(scr, rows, cols, body);
        } else if (m == AGENT) {
            draw_detail(scr, rows, cols, body);
            // progress bar (only if rows allow) + tool-step ticks
            if (rows >= 6) {
                int bar_row = rows - 2;
                int filled = (progress * (cols-2)) / 100;
                char bar[32]; int bi = 0; bar[bi++] = '[';
                for (int i = 0; i < cols-2; ++i) bar[bi++] = (i < filled) ? '#' : '-';
                bar[bi++] = ']'; bar[bi] = 0; trim(bar, cols);
                scr.draw_text(0, bar_row, bar);
                // steps: last up-to-4 ticks joined
                char st[32]; int si = 0;
                int start = step_n > 4 ? step_n - 4 : 0;
                for (int i = start; i < step_n; ++i) {
                    si += snprintf(st + si, sizeof(st) - si, "\xB7%s ", steps[i]);
                }
                trim(st, cols); scr.draw_text(0, rows-1, st);
            }
        } else if (m == TRANSCRIBE) {
            ++rec_pulse;
            const char* blk = (rec_pulse % 16) < 8 ? "\xE2\x96\x88" : "\xE2\x96\x91"; // █ / ░
            char ln[32]; snprintf(ln, sizeof(ln), "REC %d:%02d%s", rec_secs/60, rec_secs%60, blk);
            scr.draw_text(0, body, ln); body++;
            draw_detail(scr, rows, cols, body);
        } else if (m == HEALTH) {
            char ln[32];
            snprintf(ln, sizeof(ln), "HR %d  SpO2 %d%%", hr, spo2); scr.draw_text(0, body, ln);
            snprintf(ln, sizeof(ln), "ring %dmV bead %dmV", ring_batt, bead_batt); scr.draw_text(0, body+1, ln);
            // pixel graphics on capable panels (>=64px wide): HR + SpO2 arcs + batt icon
            // skip when battery is low (<30%) to save power — text above still shows
            bool low_power = (bead_batt > 0 && bead_batt < 30) || (ring_batt > 0 && ring_batt < 30);
            if (scr.w() >= 64 && scr.h() >= 48 && !low_power) {
                int cx = scr.w() / 2;
                drawGauge(scr, cx - 18, body + 18, 14, hr > 0 ? (hr * 100 / 200) : 0);
                drawGauge(scr, cx + 18, body + 18, 14, spo2);
                drawBatteryIcon(scr, 2, scr.h() - 10, ring_batt, bead_batt, charging, ++low_frame);
            }
        } else if (m == NAV) {
            char ln[32]; snprintf(ln, sizeof(ln), "%s %dm", nav_arrow(nav_head), nav_dist); scr.draw_text(0,body,ln);
            scr.draw_text(0,body+1,nav_label);
        } else if (m == TELEPROMPTER) {
            char ln[32]; snprintf(ln, sizeof(ln), "TELE %d", tele_page); scr.draw_text(0,body,ln);
            draw_detail(scr, rows, cols, body+1);
        } else if (m == SETTINGS) {
            scr.draw_text(0,body,"Settings");
            scr.draw_text(0,body+1,"A:back");
        } else if (m == CONFIRM) {
            scr.draw_text(0,body,confirm_prompt);
            scr.draw_text(0,body+1,"A:yes  B:no");
        } else if (m == CHOICE) {
            char hdr[32]; snprintf(hdr, sizeof(hdr), "choose [%s]", choice_cb);
            trim(hdr, cols); scr.draw_text(0, body, hdr); body++;
            for (int i = 0; i < rows-2 && i < choice_n; ++i) {
                const char* mk = (i == choice_sel) ? ">" : " ";
                char ln[40]; snprintf(ln, sizeof(ln), "%s%d %s", mk, i+1, choices[i]);
                trim(ln, cols); scr.draw_text(0, body+i, ln);
            }
            scr.draw_text(0, rows-1, "wheel:pick A:ok B:back");
        }
        // transient toast overlay (last row) wins over body content
        if (toast_ttl > 0) {
            char ln[TOAST + 2]; snprintf(ln, sizeof(ln), "* %s", toast_msg); // "* " + 47-char max msg + nul = 50
            trim(ln, cols); scr.draw_text(0, rows-1, ln);
        }
        scr.flush();
    }

    // Public: human-readable mode label (also used by host/serial debug).
    static const char* mode_name(Mode m) {
        switch (m) {
            case HOME: return "HOME"; case MENU: return "MENU"; case NOTES: return "NOTES";
            case NOTE_DETAIL: return "NOTE"; case TRANSCRIBE: return "REC"; case TRANSLATE: return "TR";
            case HEALTH: return "HLTH"; case TELEPROMPTER: return "TELE"; case NAV: return "NAV";
            case CAMERA: return "CAM"; case IMAGE_ANALYSIS: return "IMG"; case SSH: return "SSH";
            case SETTINGS: return "CFG"; case CONFIRM: return "?"; case CHOICE: return "CHO"; case AGENT: return "AGENT";
        }
        return "";
    }

private:
    static int clamp(int v, int lo, int hi) { if (v<lo) v=lo; if (v>hi) v=hi; return v; }
    static void trim(char* s, int cols) { if ((int)strlen(s) > cols) s[cols]=0; }
    static const char* trunc(const char* s, int cols) { static char b[128]; int n=0; while (s[n] && n<cols && n<127) { b[n]=s[n]; ++n; } b[n]=0; return b; }
    static const char* nav_arrow(int deg) {
        // 8-point compass arrow from heading (0=N). Pure glyph, BOM-free.
        static const char* arrows[8] = {"\x18","\x1E","\x1B","\x1F","\x19","\x11","\x1A","\x17"};
        int i = ((deg % 360) + 360) % 360;
        return arrows[(i + 22) / 45 % 8];
    }
    template<typename S>
    void draw_detail(S& scr, int rows, int cols, int start_row) {
        // word-aware wrap (no mid-word splits) for agent answers on tiny panels
        int r = start_row;
        int p = scroll_off;
        while (p < detail_len && r < rows) {
            // find line end: up to cols chars, break at last space before cols
            int line_end = p;
            int last_space = -1;
            int n = 0;
            while (p + n < detail_len && n < cols) {
                char c = detail[p + n];
                if (c == '\n') { line_end = p + n; break; }
                if (c == ' ') last_space = p + n;
                line_end = p + n + 1;
                ++n;
            }
            if (line_end == p + n) { /* hit cols */
                if (last_space > p && detail[p + n] != ' ') line_end = last_space + 1;
            }
            char ln[64];
            int i = 0;
            while (p < line_end && detail[p] != '\n' && i < 63) ln[i++] = detail[p++];
            if (p < detail_len && detail[p] == '\n') ++p;
            else if (p < detail_len && detail[p] == ' ') ++p;  // swallow wrap-space
            ln[i] = 0;
            scr.draw_text(0, r, ln);
            ++r;
        }
    }
    void cmd(uint8_t a, const char* arg = nullptr) { if (send_cmd) send_cmd(a, arg ? arg : ""); }
};

} // namespace cyclops
#endif
